BBUK/Bell-Boy/images/BBstack.png

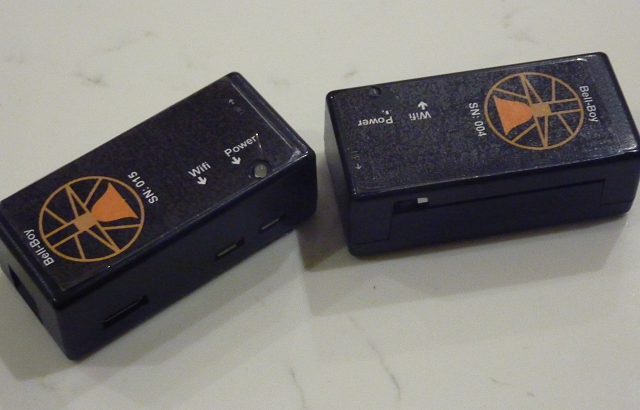
images/BBstack.png
