BBUK/Bell-Boy/images/Bootloading.png

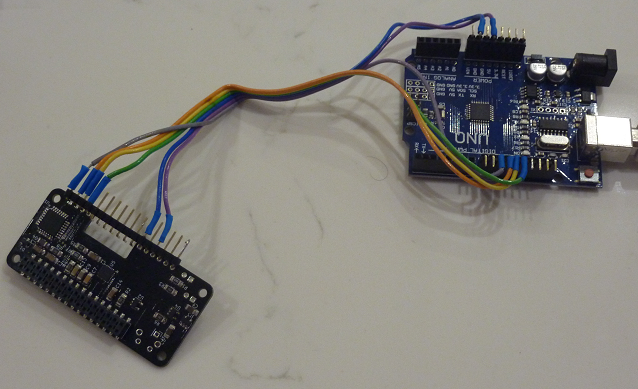
images/Bootloading.png
