BBUK/Bell-Boy/images/case.png

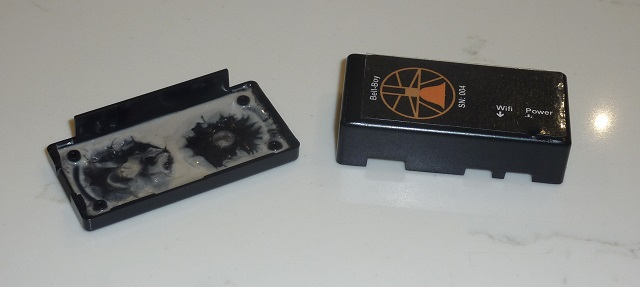
images/case.png
