BBUK/Bell-Boy/images/CompletedHeader.png

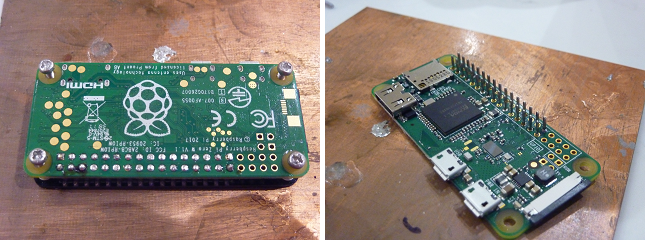
images/CompletedHeader.png
