BBUK/Bell-Boy/images/CompletedPCB.png

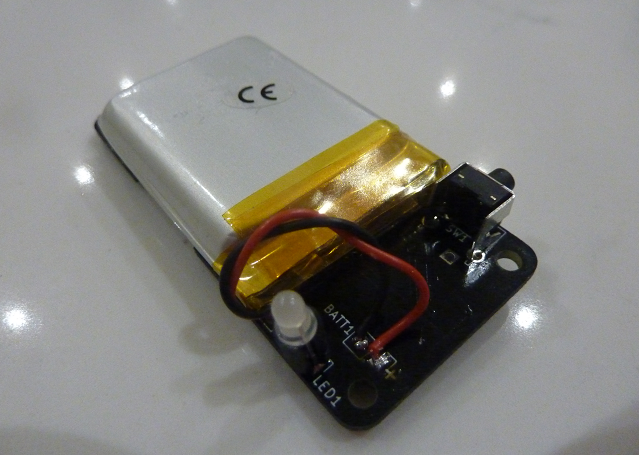
images/CompletedPCB.png
