BBUK/Bell-Boy/images/Diagnostics.png

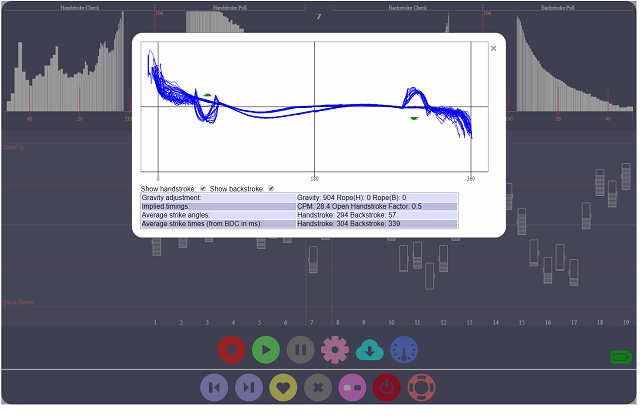
images/Diagnostics.png
