BBUK/Bell-Boy/images/DifferentDevices.png

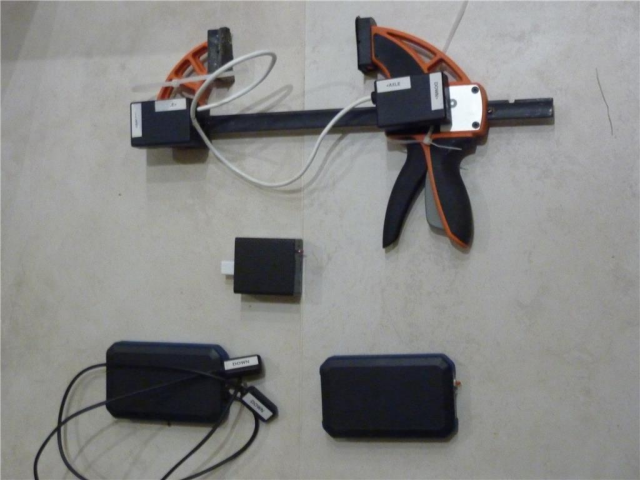
images/DifferentDevices.png
