BBUK/Bell-Boy/images/figure_1.png

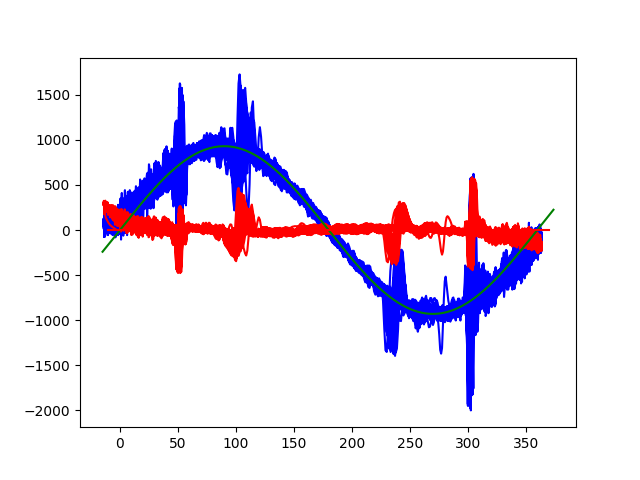
images/figure_1.png
