BBUK/Bell-Boy/images/figure_2.png

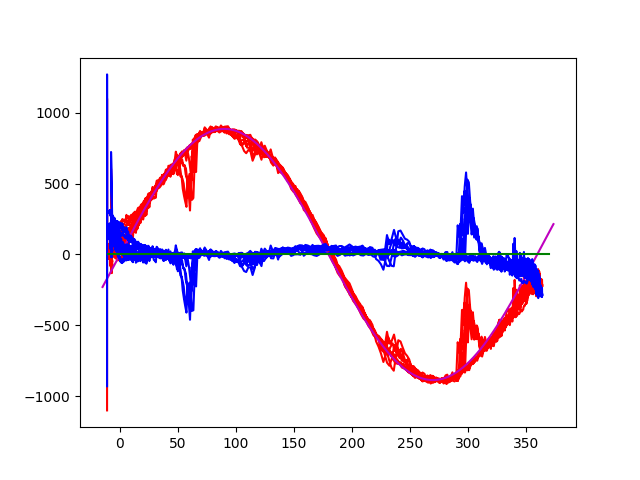
images/figure_2.png
