BBUK/Bell-Boy/images/figure_3.png

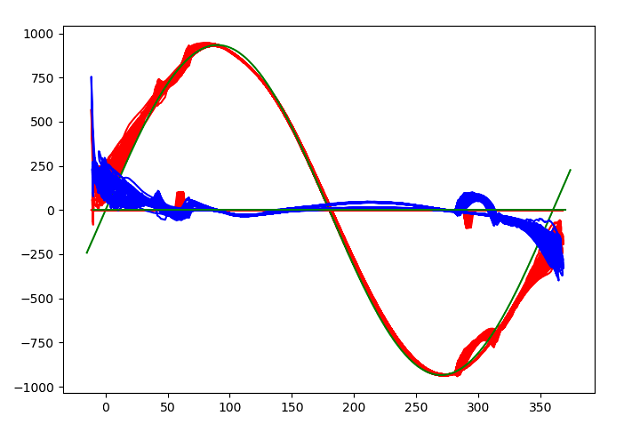
images/figure_3.png
