BBUK/Bell-Boy/images/filescreen.png

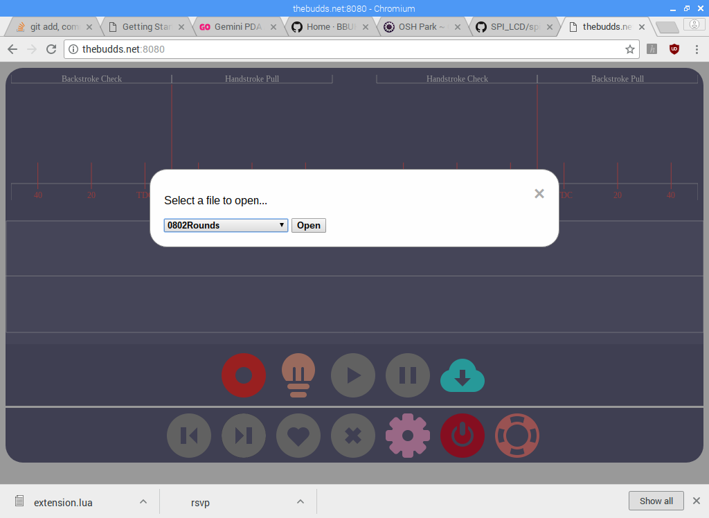
images/filescreen.png
