BBUK/Bell-Boy/images/hotplate.png

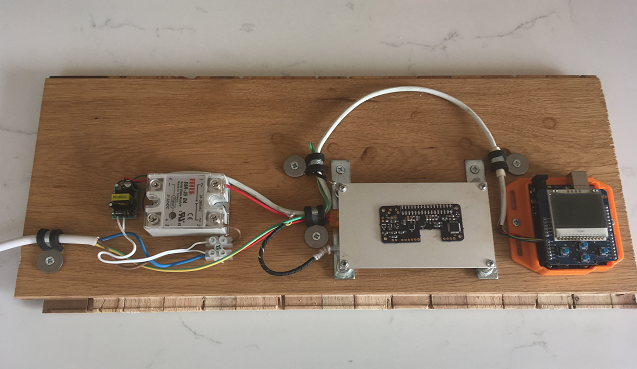
images/hotplate.png
