BBUK/Bell-Boy/images/InitialData.png

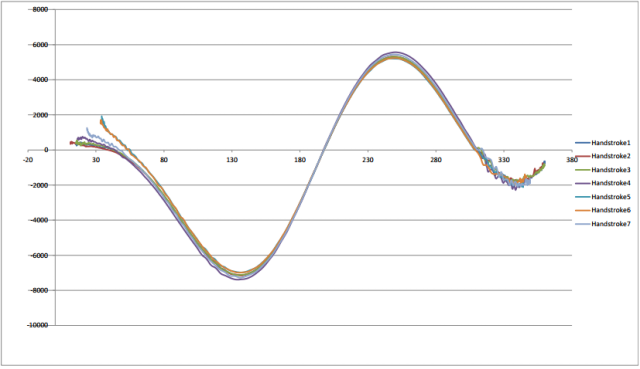
images/InitialData.png
