BBUK/Bell-Boy/images/Internals.png

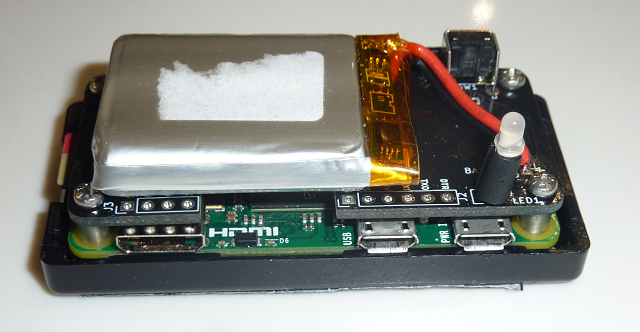
images/Internals.png
