BBUK/Bell-Boy/images/LEDPositioning.png

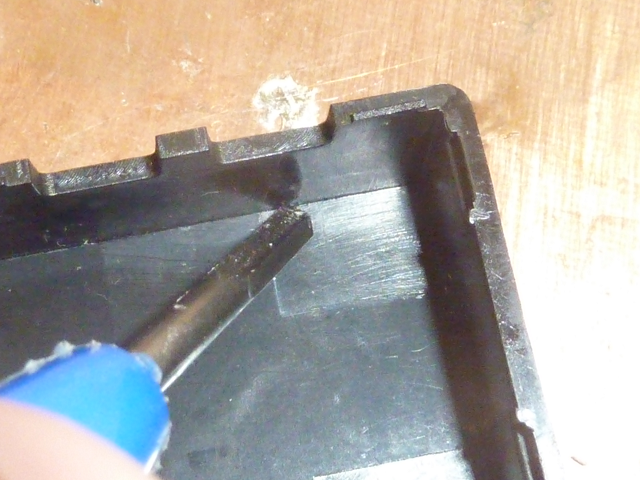
images/LEDPositioning.png
