BBUK/Bell-Boy/images/OtherEffects.png

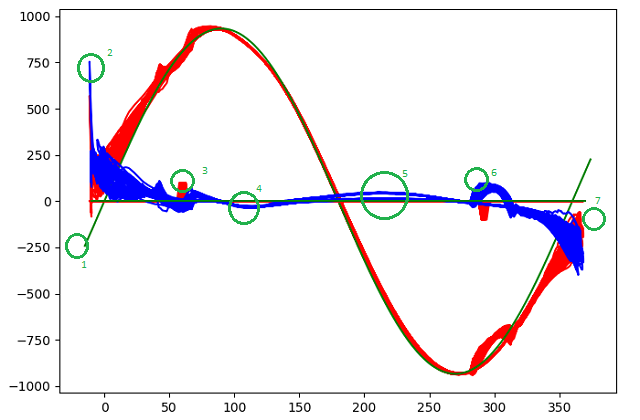
images/OtherEffects.png
