BBUK/Bell-Boy/images/PCB2.png

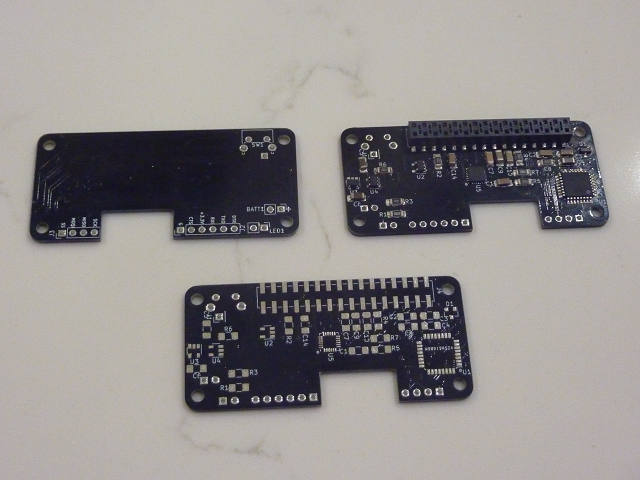
images/PCB2.png
