BBUK/Bell-Boy/images/PCBHeader.png

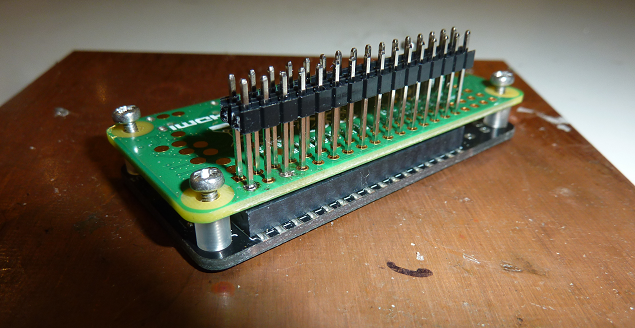
images/PCBHeader.png
