BBUK/Bell-Boy/images/PCBs.png

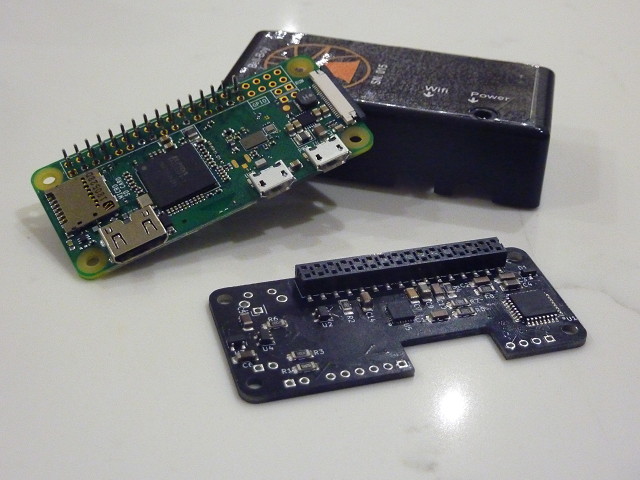
images/PCBs.png
