BBUK/Bell-Boy/images/PlainHunt.png

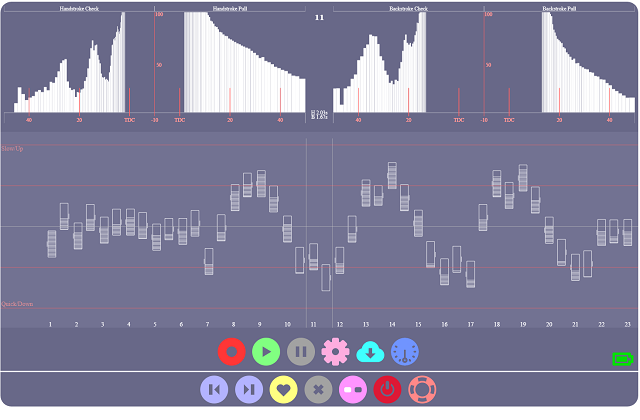
images/PlainHunt.png
