BBUK/Bell-Boy/images/Playback.png

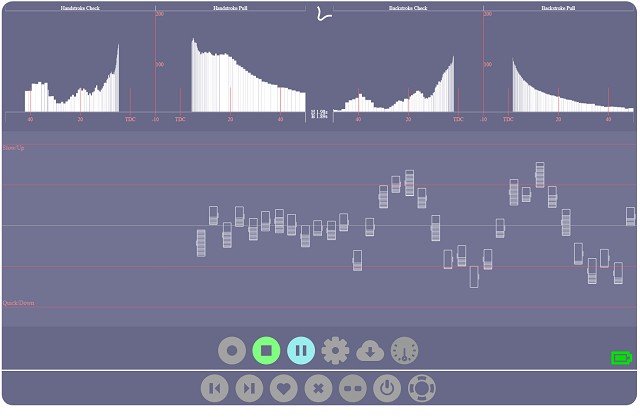
images/Playback.png
