BBUK/Bell-Boy/images/Programming.png

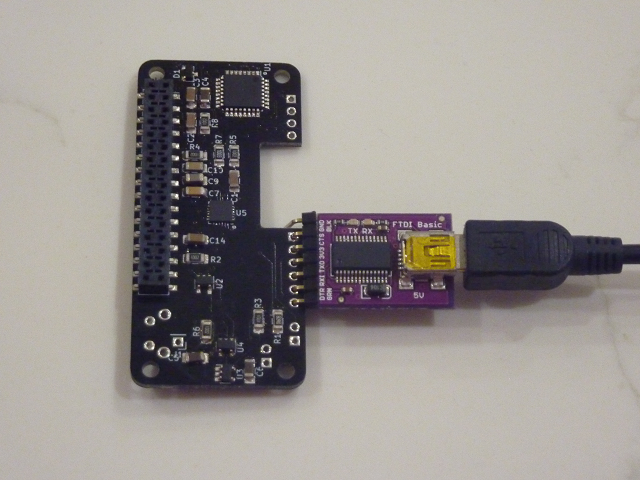
images/Programming.png
