BBUK/Bell-Boy/images/recordscreen.png

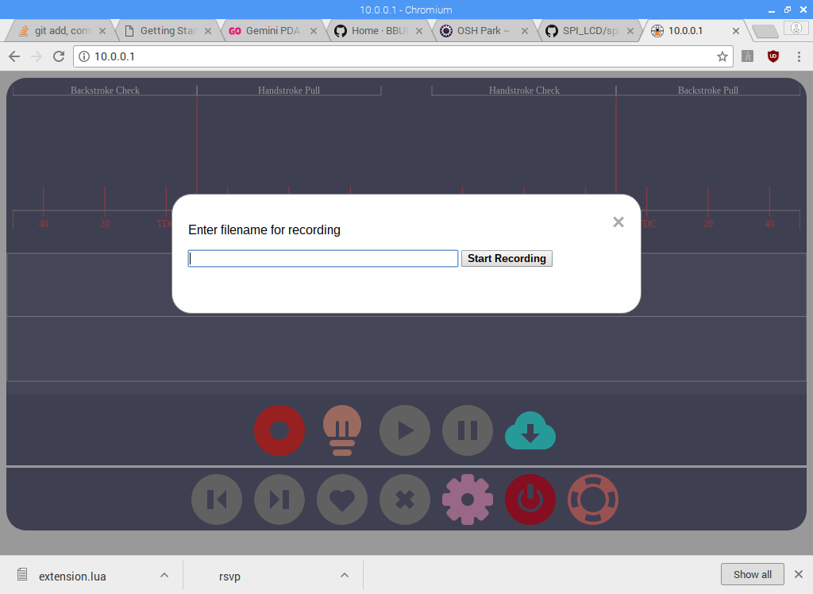
images/recordscreen.png
