BBUK/Bell-Boy/images/Settings.png

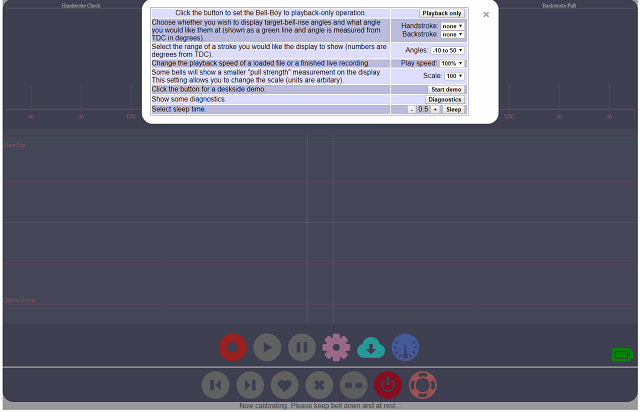
images/Settings.png
