BBUK/Bell-Boy/images/StayBounce.png

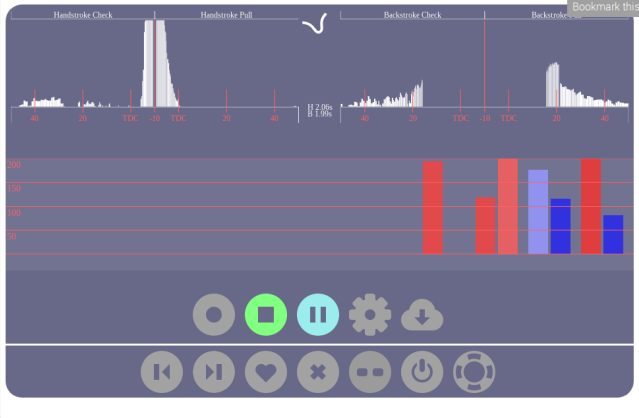
images/StayBounce.png
