BBUK/Bell-Boy/images/StrokeByStroke.png

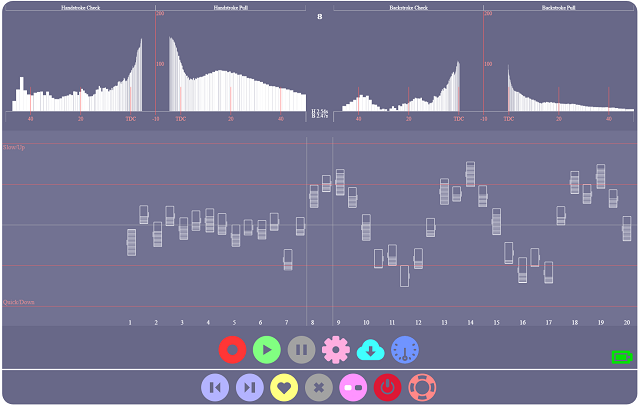
images/StrokeByStroke.png
