BBUK/Bell-Boy/images/Timings.png

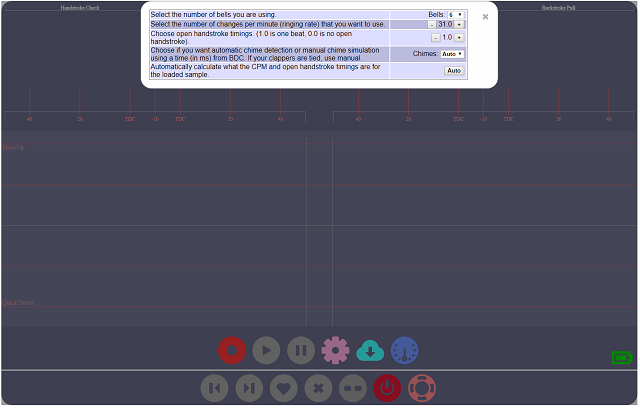
images/Timings.png
