BBUK/Bell-Boy/images/v1v2.png

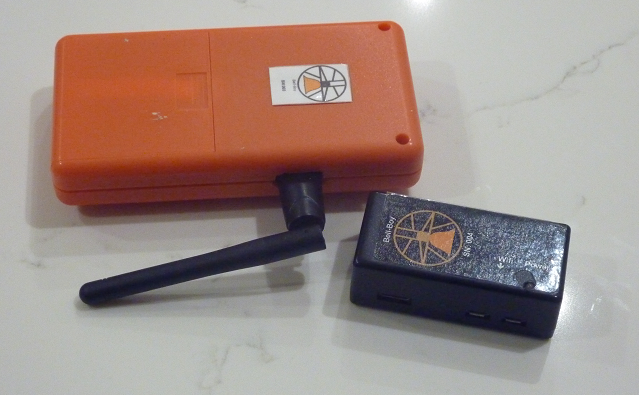
images/v1v2.png
