BBUK/Bell-Boy/images/wifistick.png

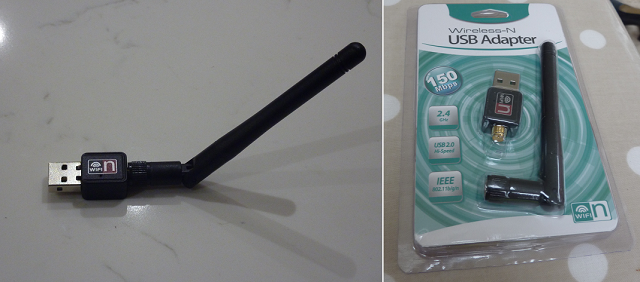
images/wifistick.png
