BBUK/Bell-Boy/images/MainScreenGuide.png

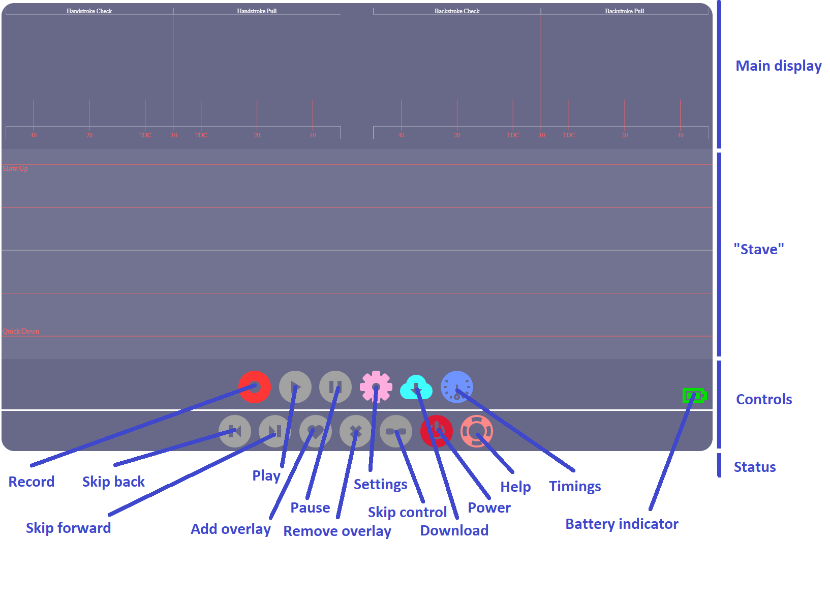
images/MainScreenGuide.png
